galah-x/DamLevelSensor/damlevelsensor/addresses.h

//    -*- Mode: c++     -*-
// emacs automagically updates the timestamp field on save
// my $ver =  'dam sonar level sensor  Time-stamp: "2023-07-28 17:20:38 john"';

// radio addresses 
const uint8_t RELAY   = 0x81;   // relay on the roof to homenet
const uint8_t LOGGER  = 0x02;   // homenet logger
const uint8_t NODEID  = 0x88;   // the dam sensor 
